DWestbury-PP/evo64/3D-printables/LCD 20x4 Mount - Rounded/4x20 LCD Box/lcdbox.obj

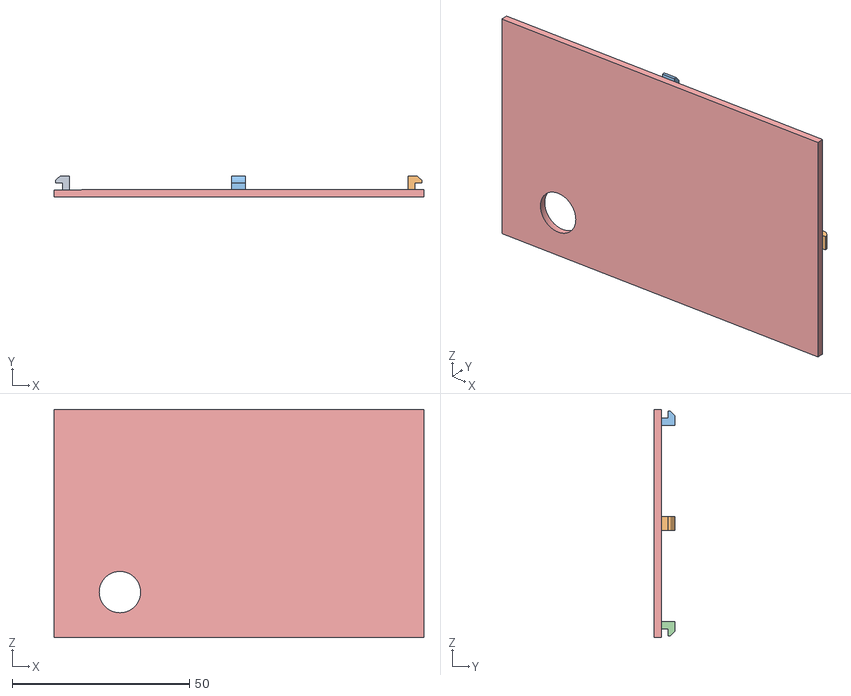
[picture p65: CAD file, 2025-09-21]
3D-printables/LCD 20x4 Mount - Rounded/4x20 LCD Box/lcdbox.obj
104.5 x 5.84 x 64.5
latch_4
latch_3
latch_2
latch_1
Bottom
