DWestbury-PP/evo64/3D-printables/LCD 20x4 Mount - Rounded/4x20 LCD Box/lcdbox_stand.obj

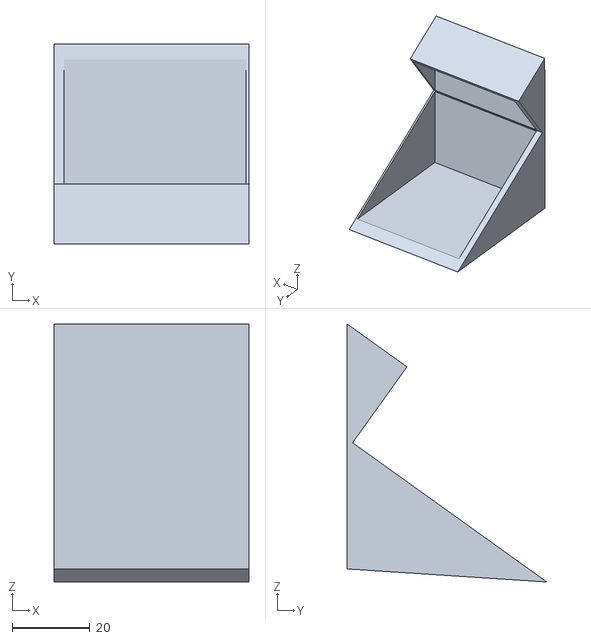
[picture p66: CAD file, 2025-09-21]
3D-printables/LCD 20x4 Mount - Rounded/4x20 LCD Box/lcdbox_stand.obj
50.0 x 51.3 x 66.2
